Megazoids-Hut/MegaPocket/images/1.jpg

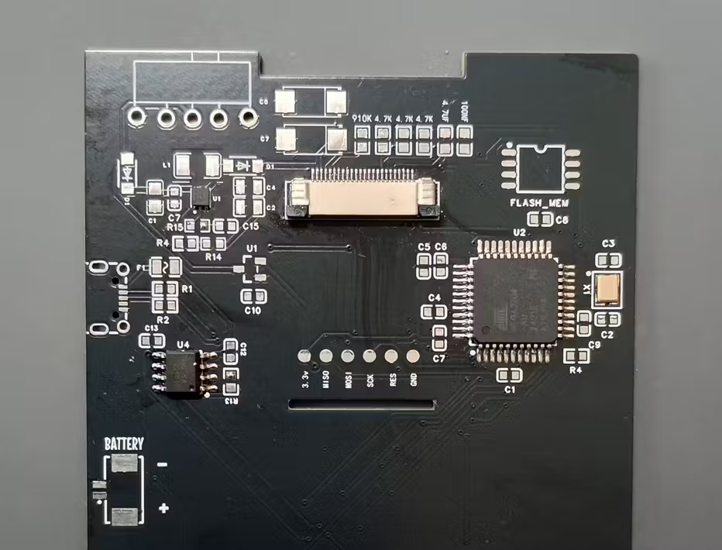
images/1.jpg
