Megazoids-Hut/MegaPocket/images/2.jpg

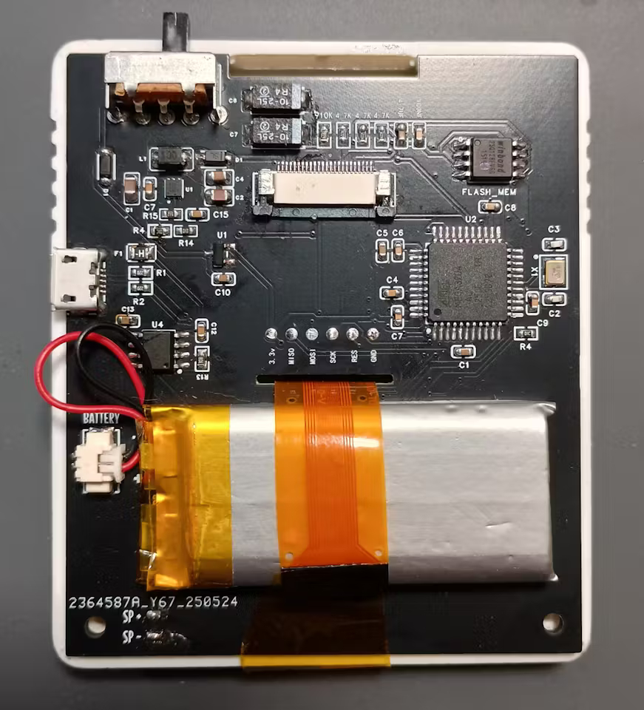
images/2.jpg
