Megazoids-Hut/MegaPocket/images/3.jpg

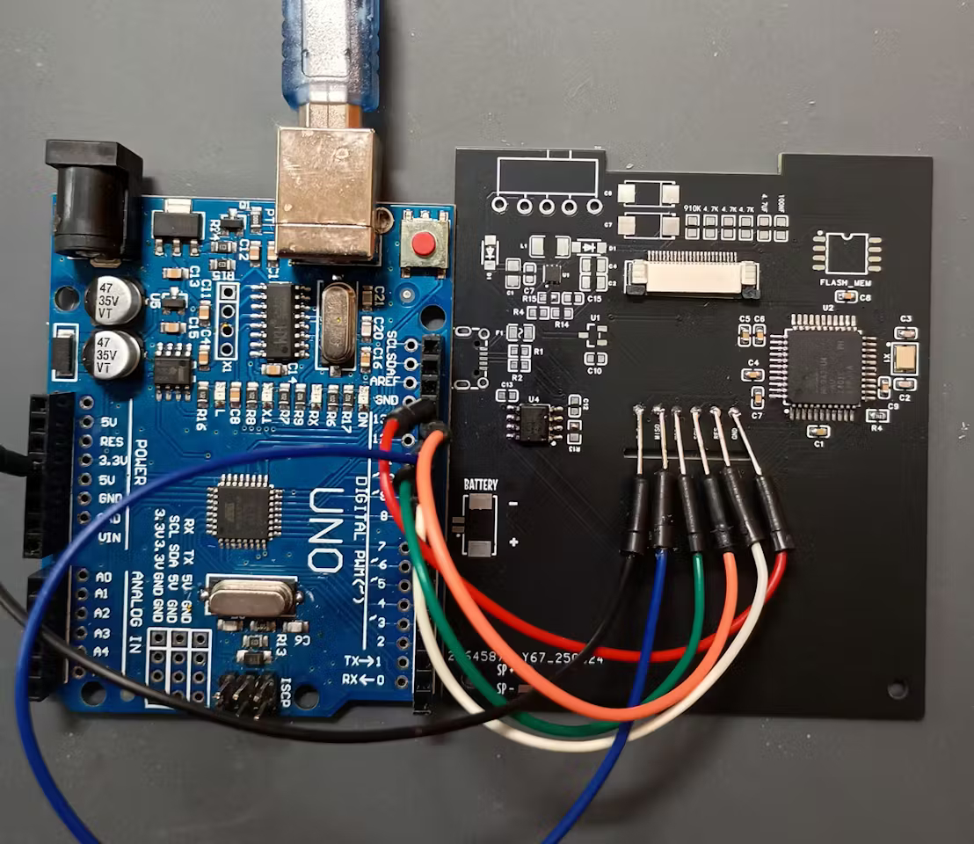
images/3.jpg
