Megazoids-Hut/MegaPocket/images/4.jpg

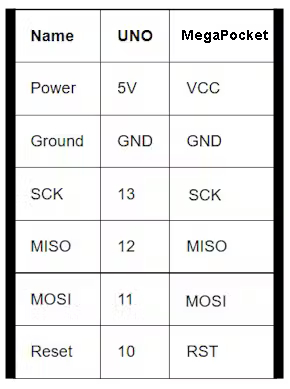
images/4.jpg
