Megazoids-Hut/MegaPocket/images/5.jpg

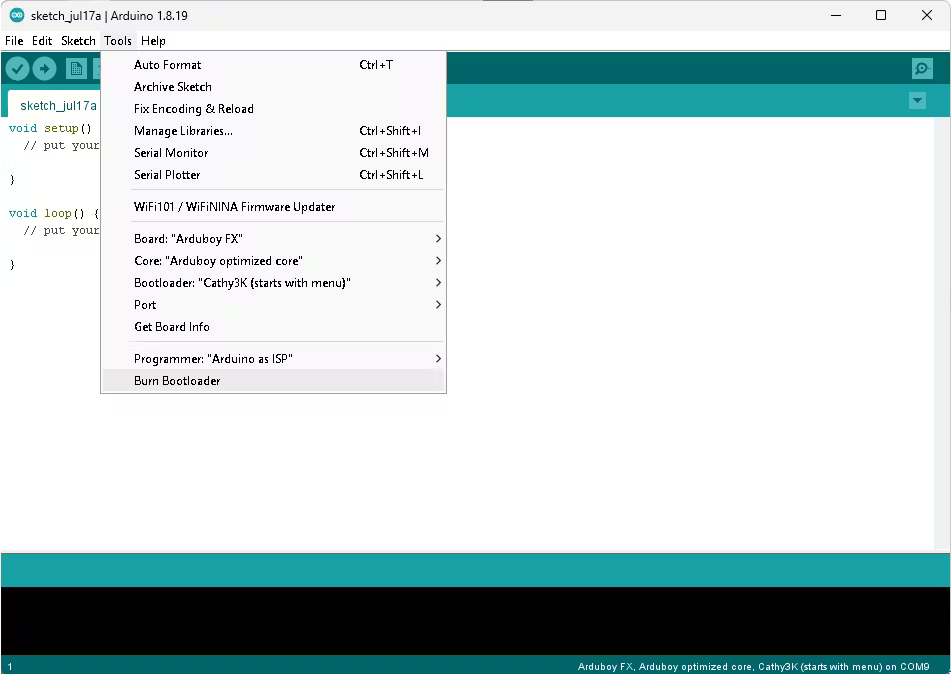
images/5.jpg
