Megazoids-Hut/MegaPocket/images/6.jpg

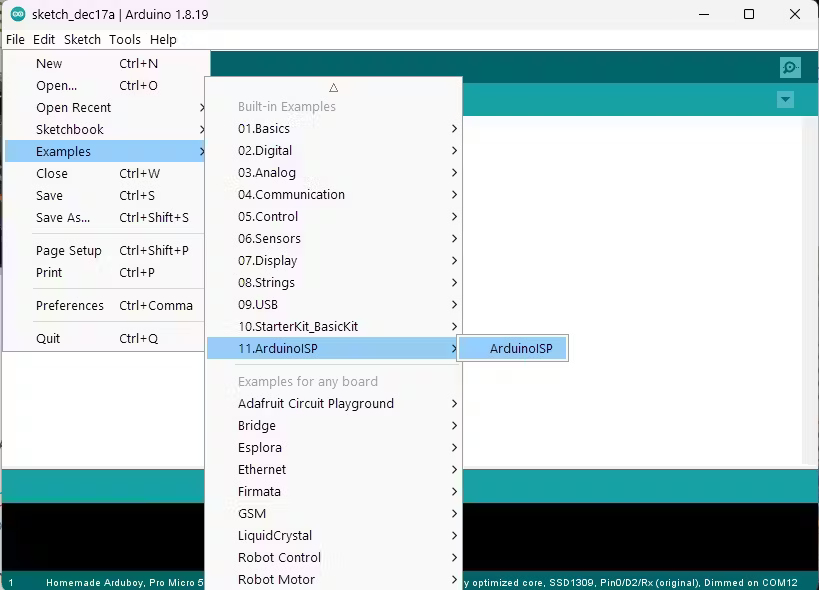
images/6.jpg
