Megazoids-Hut/MegaPocket/images/7.jpg

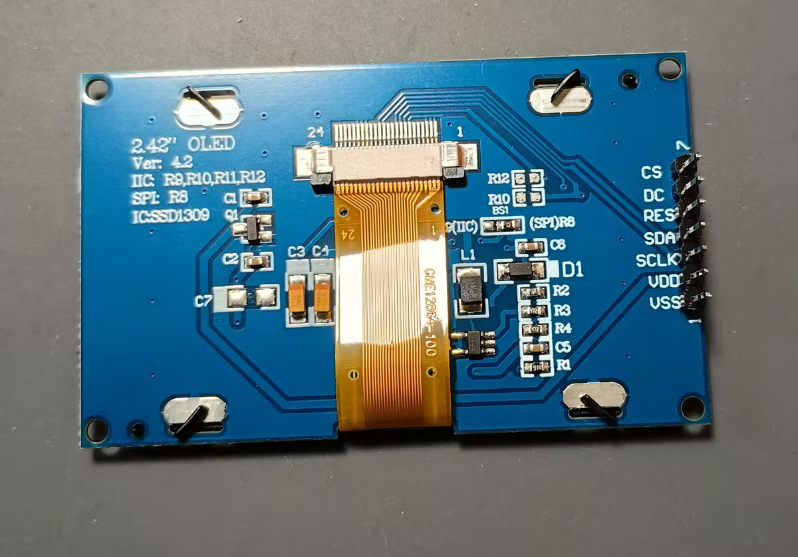
images/7.jpg
