Megazoids-Hut/MegaPocket/images/8.jpg

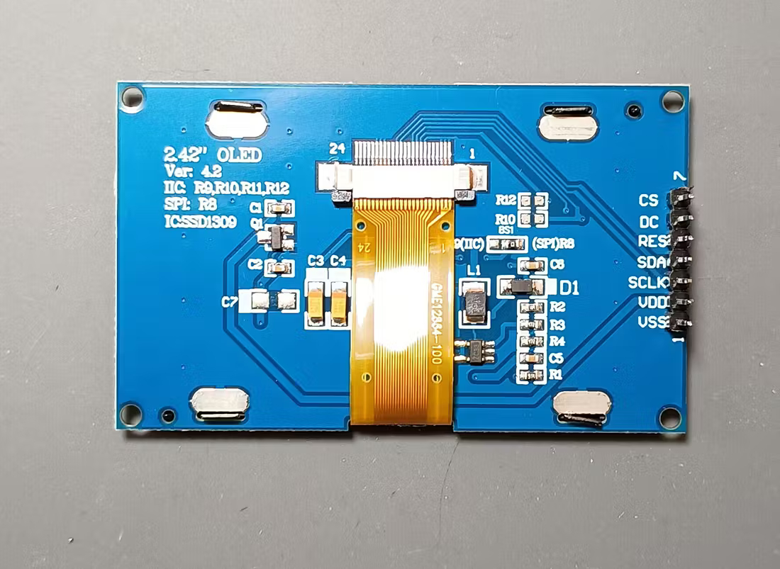
images/8.jpg
