Megazoids-Hut/MegaPocket/images/9.jpg

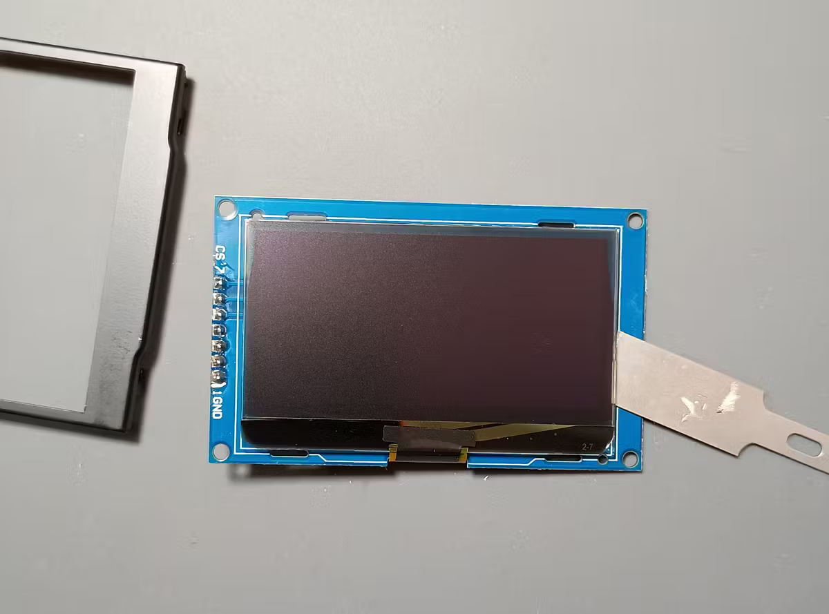
images/9.jpg
