Megazoids-Hut/MegaPocket/images/10.jpg

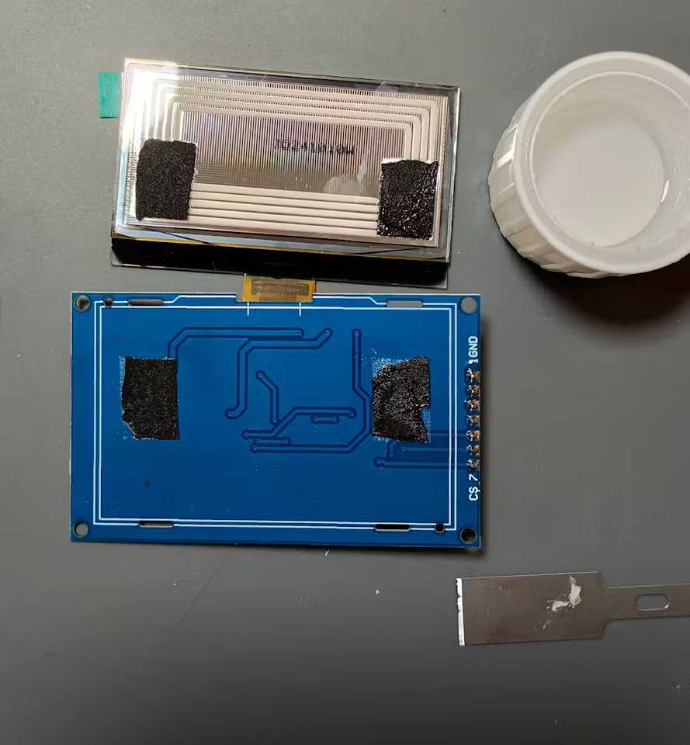
images/10.jpg
