Megazoids-Hut/MegaPocket/images/11.jpg

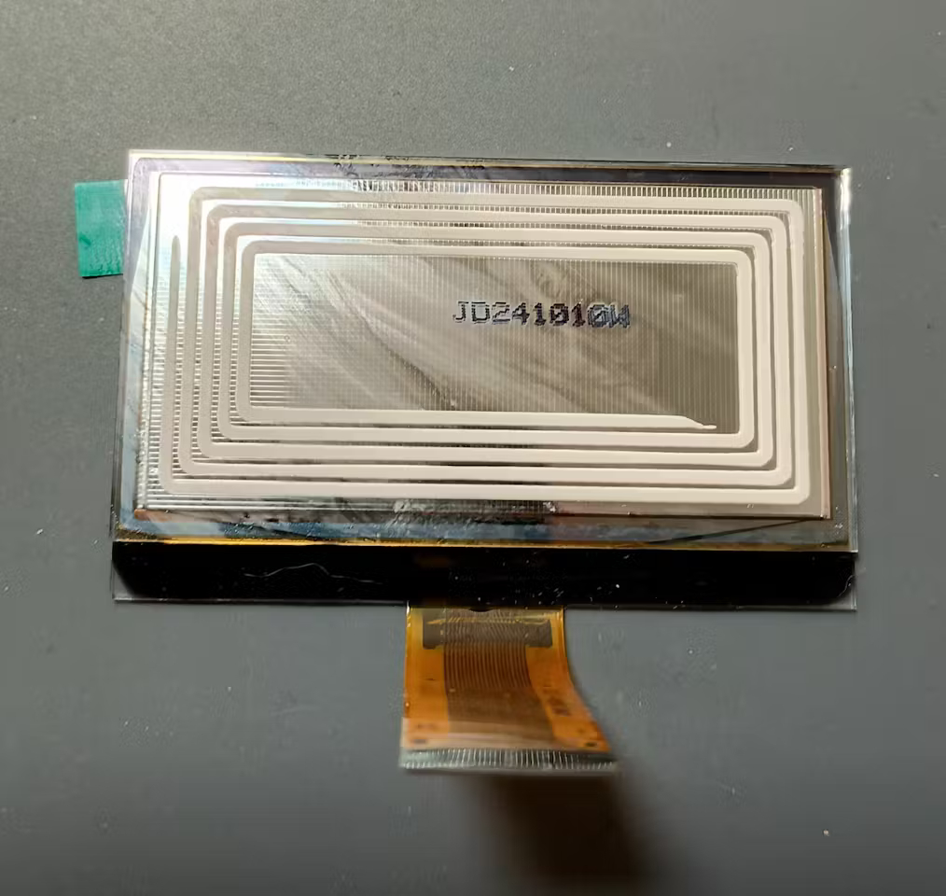
images/11.jpg
