Megazoids-Hut/MegaPocket/images/12.jpg

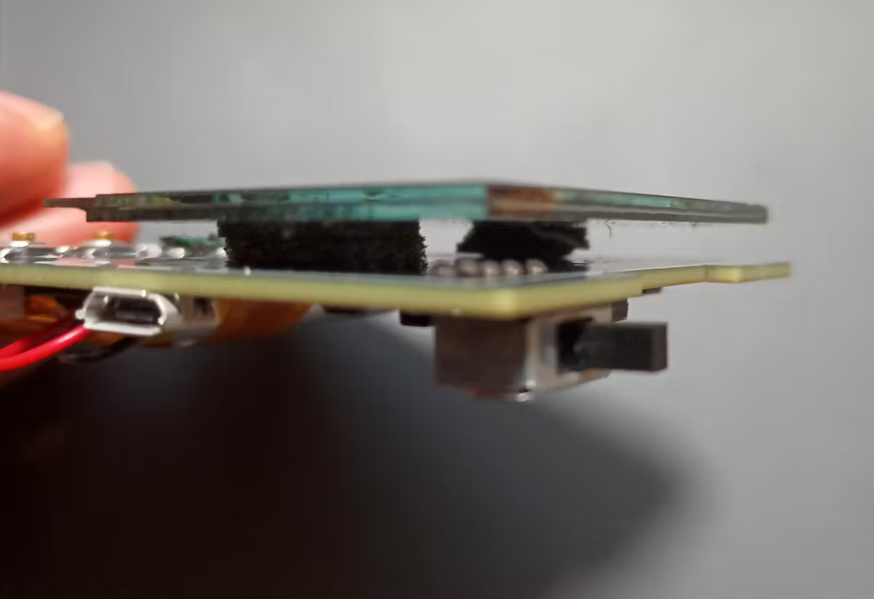
images/12.jpg
