Megazoids-Hut/MegaPocket/images/13.jpg

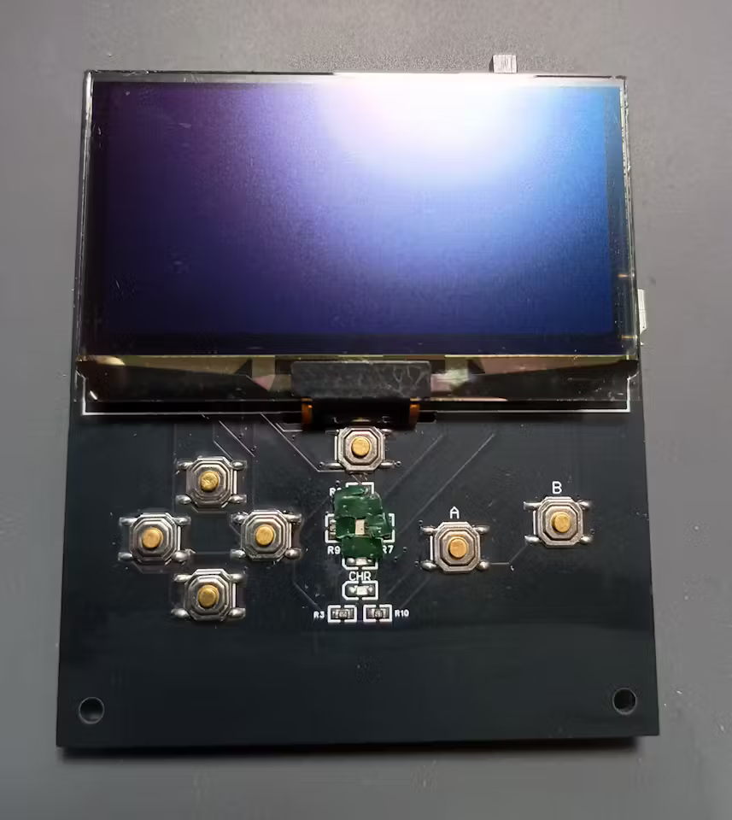
images/13.jpg
