Megazoids-Hut/MegaPocket/images/14.jpg

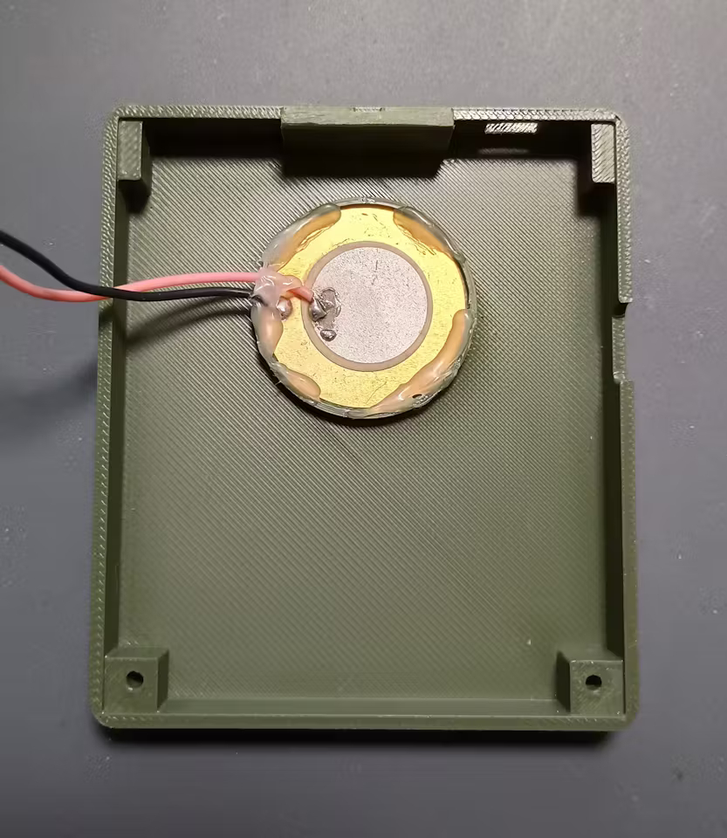
images/14.jpg
