Megazoids-Hut/MegaPocket/images/15.jpg

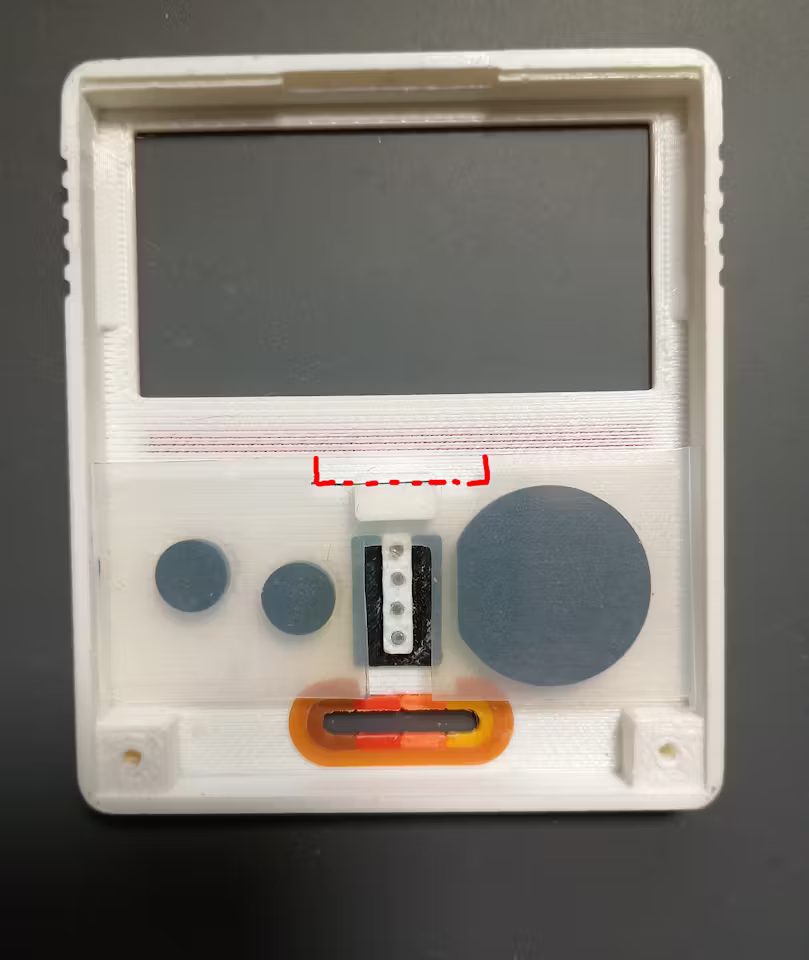
images/15.jpg
