Megazoids-Hut/MegaPocket/images/16.jpg

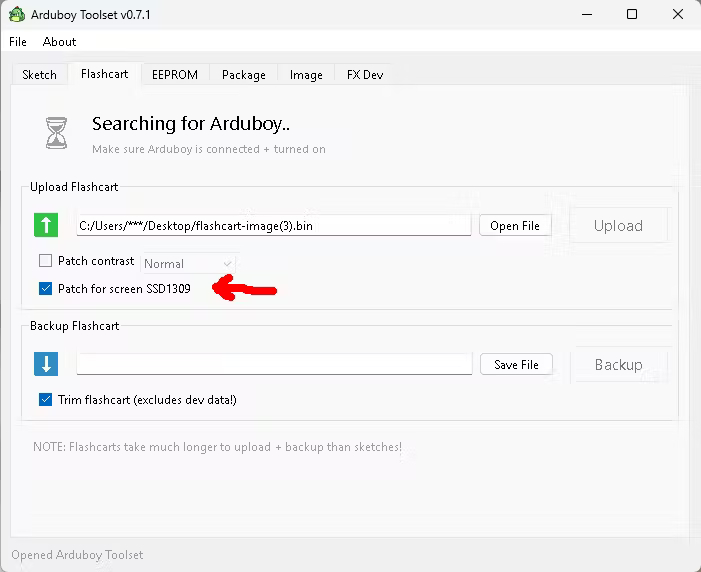
images/16.jpg
