Megazoids-Hut/MegaPocket/images/mp1.jpg

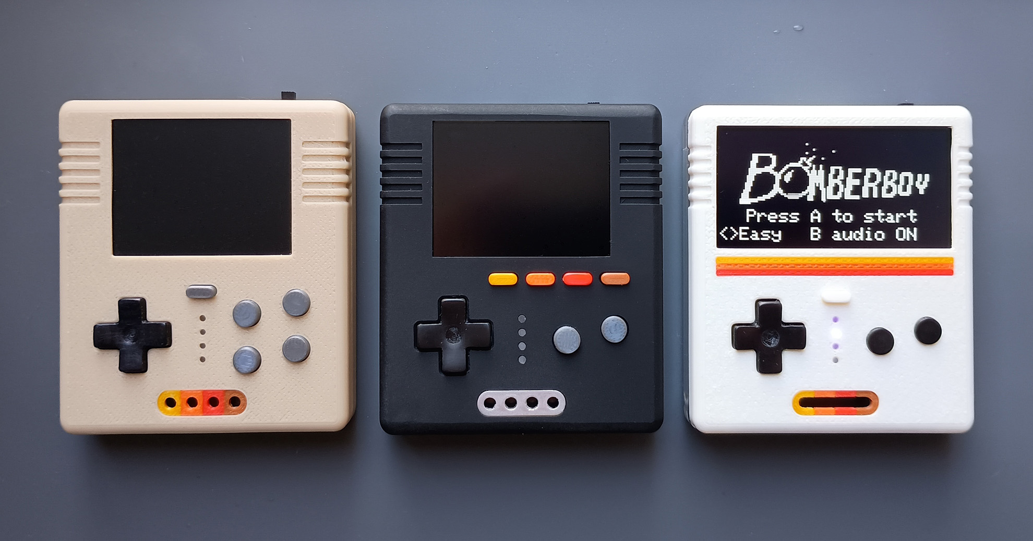
images/mp1.jpg
